PMY9527/GIP-Group-9-Respository/Extraction Mechanism/CAD/Screenshot 2024-04-28 at 22.20.18.png

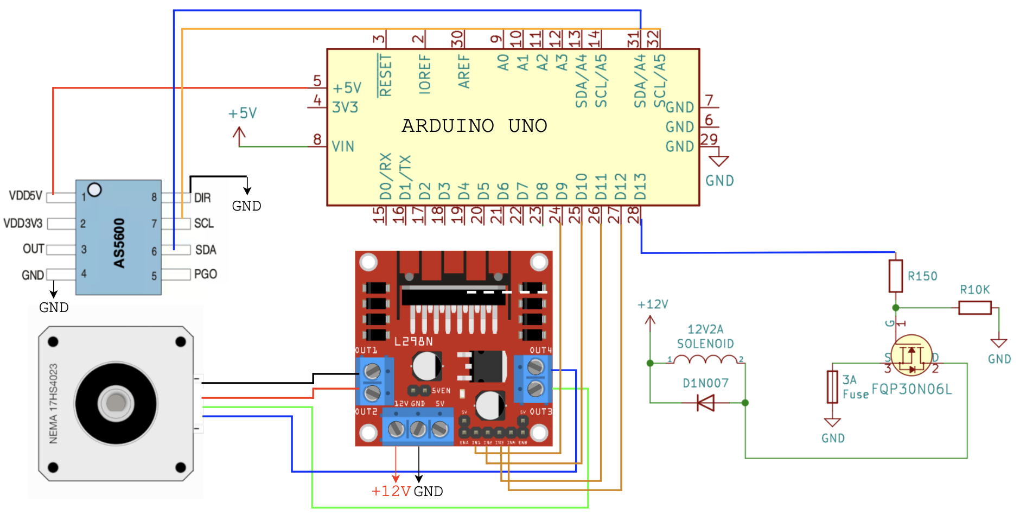
Extraction Mechanism/CAD/Screenshot 2024-04-28 at 22.20.18.png
