PMY9527/GIP-Group-9-Respository/Extraction Mechanism/MATLAB:SIMULINK/Kalman/kalman.jpg

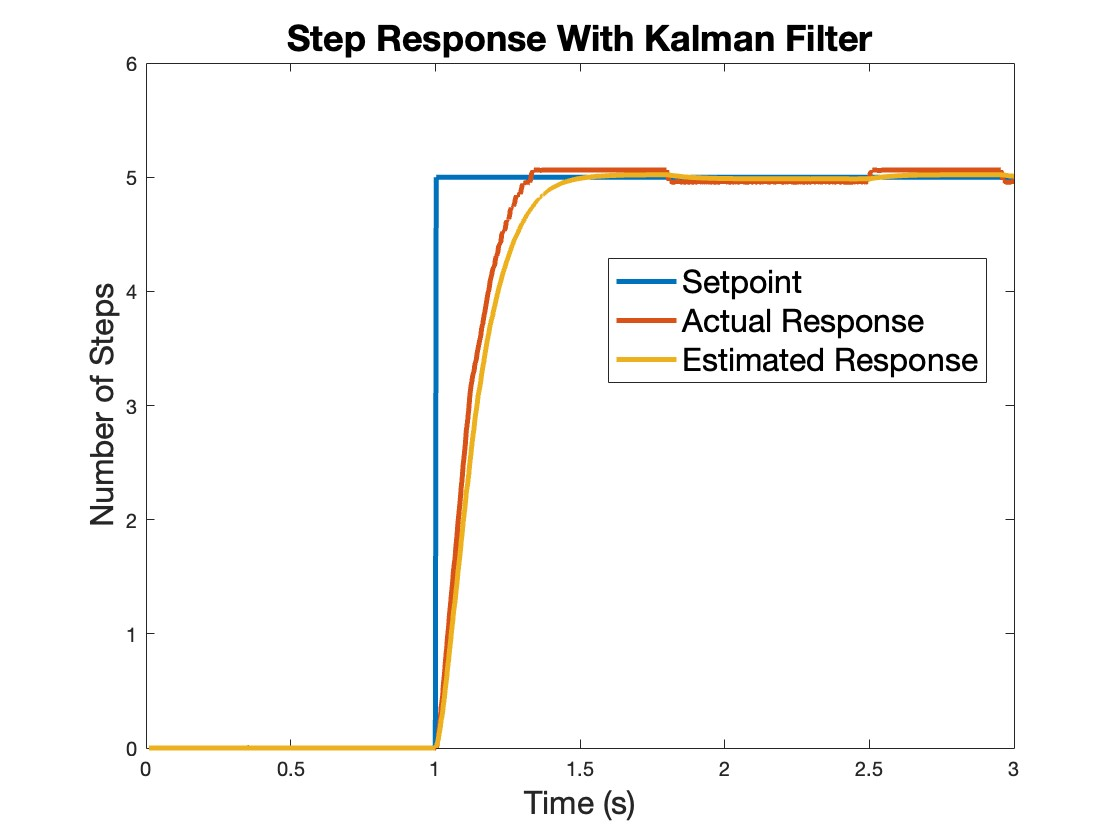
Extraction Mechanism/MATLAB:SIMULINK/Kalman/kalman.jpg
