PMY9527/GIP-Group-9-Respository/Extraction Mechanism/MATLAB:SIMULINK/Kalman/withkalman.png

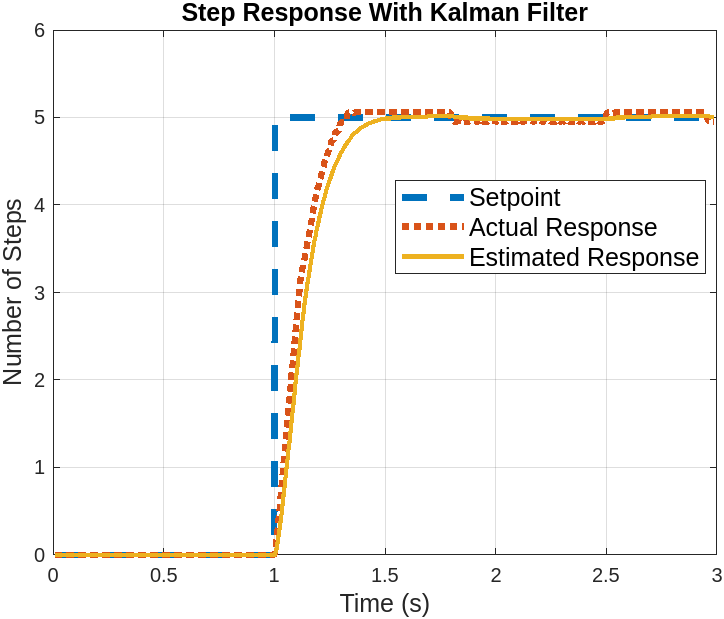
Extraction Mechanism/MATLAB:SIMULINK/Kalman/withkalman.png
