PMY9527/GIP-Group-9-Respository/Extraction Mechanism/MATLAB:SIMULINK/LQR/LQR.jpg

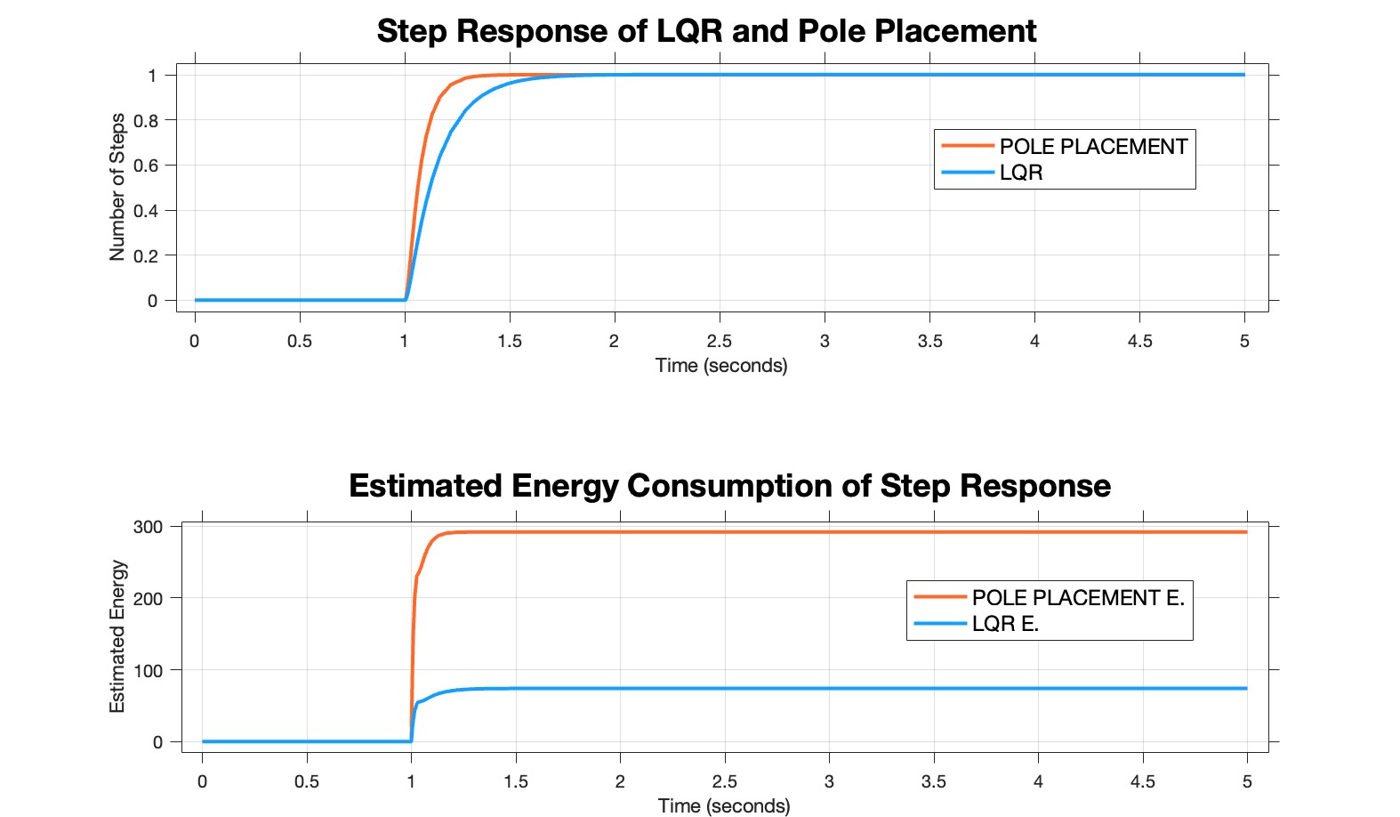
Extraction Mechanism/MATLAB:SIMULINK/LQR/LQR.jpg
