PMY9527/GIP-Group-9-Respository/Extraction Mechanism/MATLAB:SIMULINK/MPC/mpc.png

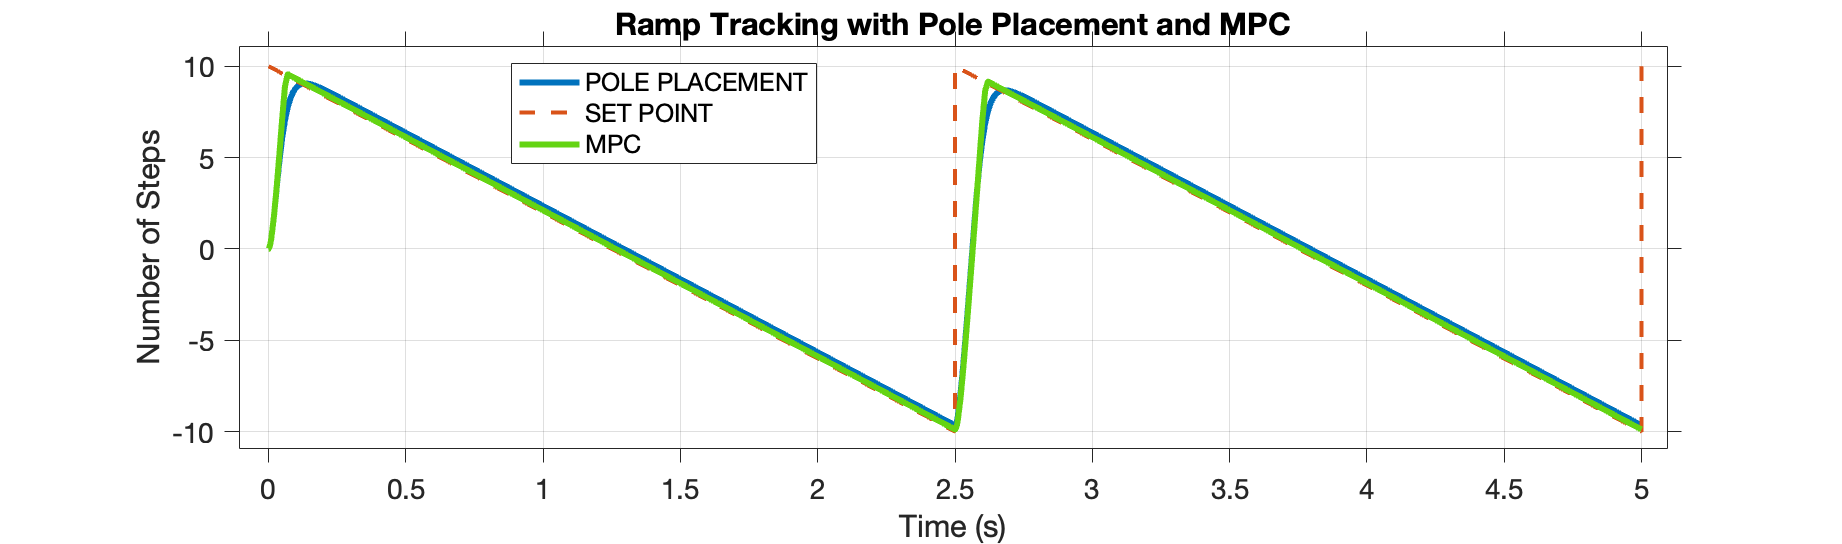
Extraction Mechanism/MATLAB:SIMULINK/MPC/mpc.png
